Armencho2012/Aido-v1/Robot codes/icons.py

"""
╔══════════════════════════════════════════════════════╗
║       AIDO OS — Bitmap Icon Library (8x8 & 16x16)    ║
║           Hand-crafted pixel art for menus            ║
╚══════════════════════════════════════════════════════╝
Each icon is stored as a bytearray for efficient memory use.
Format: 1 bit per pixel, row-major, MSB first.
"""
import framebuf
ICON_ANALYSE = bytearray([
    0b00000000, 0b00000000,
    0b00111111, 0b11111100,
    0b00100000, 0b00000100,
    0b00101010, 0b10100100,
    0b00100000, 0b00000100,
    0b00101111, 0b10000100,
    0b00100000, 0b00000100,
    0b00101111, 0b11100100,
    0b00100000, 0b00000100,
    0b00101111, 0b00000100,
    0b00100000, 0b00000100,
    0b00111111, 0b11111100,
    0b00000000, 0b01100000,
    0b00000000, 0b00110000,
    0b00000000, 0b00011000,
    0b00000000, 0b00000000,
])
ICON_CARDS = bytearray([
    0b00000000, 0b00000000,
    0b00011111, 0b11110000,
    0b00010000, 0b00010000,
    0b00010011, 0b10010000,
    0b00010000, 0b00010000,
    0b00010000, 0b00010000,
    0b00010000, 0b00010000,
    0b00010011, 0b10010000,
    0b00010000, 0b00010000,
    0b00011111, 0b11110000,
    0b00001111, 0b11111000,
    0b00001000, 0b00001000,
    0b00001000, 0b00001000,
    0b00001111, 0b11111000,
    0b00000000, 0b00000000,
    0b00000000, 0b00000000,
])
ICON_QUIZ = bytearray([
    0b00000000, 0b00000000,
    0b00000111, 0b11100000,
    0b00011100, 0b00111000,
    0b00110000, 0b00011000,
    0b00110000, 0b00001100,
    0b00000000, 0b00011100,
    0b00000000, 0b01110000,
    0b00000001, 0b11000000,
    0b00000001, 0b10000000,
    0b00000001, 0b10000000,
    0b00000000, 0b00000000,
    0b00000001, 0b10000000,
    0b00000011, 0b11000000,
    0b00000001, 0b10000000,
    0b00000000, 0b00000000,
    0b00000000, 0b00000000,
])
ICON_NEURAL = bytearray([
    0b00000000, 0b00000000,
    0b00000011, 0b11000000,
    0b00000100, 0b00100000,
    0b00001000, 0b00010000,
    0b00001000, 0b00010000,
    0b00000100, 0b00100000,
    0b01100011, 0b11000110,
    0b10010000, 0b00001001,
    0b10010000, 0b00001001,
    0b01100011, 0b11000110,
    0b00000100, 0b00100000,
    0b00001000, 0b00010000,
    0b00001000, 0b00010000,
    0b00000100, 0b00100000,
    0b00000011, 0b11000000,
    0b00000000, 0b00000000,
])
ICON_GAMES = bytearray([
    0b00000000, 0b00000000,
    0b00000000, 0b00000000,
    0b01111111, 0b11111110,
    0b11111111, 0b11111111,
    0b11000110, 0b01100011,
    0b11001110, 0b01100011,
    0b11011111, 0b01110011,
    0b11001110, 0b00111111,
    0b11000110, 0b00011011,
    0b11000000, 0b00111111,
    0b11111111, 0b11111111,
    0b01111111, 0b11111110,
    0b00011100, 0b00111000,
    0b00001100, 0b00110000,
    0b00000000, 0b00000000,
    0b00000000, 0b00000000,
])
ICON_SETTINGS = bytearray([
    0b00000000, 0b00000000,
    0b00000110, 0b01100000,
    0b00000110, 0b01100000,
    0b00011111, 0b11111000,
    0b00111111, 0b11111100,
    0b01110011, 0b11001110,
    0b01100001, 0b10000110,
    0b11100001, 0b10000111,
    0b11100001, 0b10000111,
    0b01100001, 0b10000110,
    0b01110011, 0b11001110,
    0b00111111, 0b11111100,
    0b00011111, 0b11111000,
    0b00000110, 0b01100000,
    0b00000110, 0b01100000,
    0b00000000, 0b00000000,
])
ICONS = {
    "analyse":  ICON_ANALYSE,
    "cards":    ICON_CARDS,
    "quiz":     ICON_QUIZ,
    "neural":   ICON_NEURAL,
    "games":    ICON_GAMES,
    "settings": ICON_SETTINGS,
}
def draw_icon(fb, icon_name, x, y, c=1):
    """
    Blit a 16x16 icon onto the framebuffer at position (x, y).
    """
    data = ICONS.get(icon_name)
    if data is None:
        fb.rect(x, y, 16, 16, c)
        return
    icon_fb = framebuf.FrameBuffer(data, 16, 16, framebuf.MONO_HLSB)
    if c:
        fb.blit(icon_fb, x, y, 0)
        return
    for yy in range(16):
        for xx in range(16):
            if icon_fb.pixel(xx, yy):
                fb.pixel(x + xx, y + yy, 0)
MINI_BATT = bytearray([
    0b01111100,
    0b11111110,
    0b10000010,
    0b10111010,
    0b10111010,
    0b10111010,
    0b10000010,
    0b11111110,
])
MINI_WIFI = bytearray([
    0b00011000,
    0b01100110,
    0b10000001,
    0b00111100,
    0b01000010,
    0b00011000,
    0b00000000,
    0b00011000,
])
MINI_WIFI_OFF = bytearray([
    0b10000001,
    0b01000010,
    0b00100100,
    0b00011000,
    0b00011000,
    0b00100100,
    0b01000010,
    0b10000001,
])
def draw_mini_icon(fb, icon_data, x, y):
    """Blit an 8x8 mini icon."""
    icon_fb = framebuf.FrameBuffer(bytearray(icon_data), 8, 8, framebuf.MONO_HLSB)
    fb.blit(icon_fb, x, y, 0)
